WXYC/auto-dj-arduino-switch/COMMERCIAL.md

# Commercial Licensing

This software is released under the [PolyForm Noncommercial License 1.0.0](./LICENSE). Commercial licenses are available separately.

## You do not need a commercial license

The public license already permits, free of charge and without asking us:

- **Educational institutions** — universities, colleges, schools, and their departments
- **Charitable organizations and nonprofits**, including other college and community radio stations
- **Public research organizations** and **government institutions**
- **Personal use** — study, research, experiment, hobby projects, and private entertainment

The license grants this "regardless of the source of funding or obligations resulting from the funding," so grant-funded and university-funded work is covered. If you are a student station wanting to run your own flowsheet on this, you are already licensed. Go ahead.

## You need a commercial license

If you want to use this software for a commercial purpose — including selling it, selling a service built on it, or using it internally at a for-profit company — contact us and we will work out terms.

**Contact:** legal@wxyc.org

Please include:

- Your organization
- Which repositories you're interested in
- A short description of the intended use

We are a student-run radio station, not a software vendor, and we are reasonable to deal with.

## Attribution

Whether or not you need a commercial license, the public license requires that anyone you pass the software to also receives the license text and the `Required Notice:` lines at the bottom of [LICENSE](./LICENSE). Keep them intact.
