WXYC/auto-dj-arduino-switch/auto-dj-arduino-switch/relay_monitor.cpp

#include "relay_monitor.h"

RelayMonitor::RelayMonitor(int relayPin, int ledPin, unsigned long debounceMs)
    : relayPin(relayPin)
    , ledPin(ledPin)
    , debounceMs(debounceMs)
    , debouncedState(HIGH)
    , lastReading(HIGH)
    , lastChangeTime(0)
    , changed(false)
    , ledState(LOW)
{
}

void RelayMonitor::setUp() {
    pinMode(relayPin, INPUT_PULLUP);
    debouncedState = digitalRead(relayPin);
    lastReading = debouncedState;
    ledState = debouncedState == LOW ? HIGH : LOW;
    // ledPin < 0 means "this monitor does not own an LED" (the reporter's state
    // machine drives STATUS_LED_PIN). getLedState() still works for callers that
    // want the relay-derived value.
    if (ledPin >= 0) {
        pinMode(ledPin, OUTPUT);
        digitalWrite(ledPin, ledState);
    }
}

void RelayMonitor::update() {
    update(millis(), digitalRead(relayPin));
    if (ledPin >= 0) {
        digitalWrite(ledPin, ledState);
    }
}

void RelayMonitor::update(unsigned long currentMillis, int currentReading) {
    changed = false;

    if (currentReading != lastReading) {
        lastChangeTime = currentMillis;
    }

    if ((currentMillis - lastChangeTime) > debounceMs) {
        if (currentReading != debouncedState) {
            debouncedState = currentReading;
            changed = true;
            // LED on when auto DJ is active (relay closed = LOW)
            ledState = debouncedState == LOW ? HIGH : LOW;
        }
    }

    lastReading = currentReading;
}

bool RelayMonitor::isAutoDJActive() const {
    // Relay closed (pin LOW via pullup) = AUX off = auto DJ active
    return debouncedState == LOW;
}

bool RelayMonitor::stateChanged() const {
    return changed;
}

int RelayMonitor::getLedState() const {
    return ledState;
}
